pelrun/dtv2ser/arm/Src/uart.c

/*
 * uart.c - serial hw routines
 *
 * This file is part of dtv2ser.
 * See README for copyright notice.
 *
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
 */

#include <stdint.h>

#include "usbd_cdc_if.h"

#include "board.h"

#include "uart.h"
#include "param.h"
#include "display.h"
#include "timer.h"

#define CIRCBUF_SIZE 256

typedef struct
{
  volatile uint16_t in;
  volatile uint16_t out;
  volatile uint8_t data[CIRCBUF_SIZE];
} Circular_Buffer_t;

#define CIRCBUF_LEN(c) ((uint16_t)(c.in - c.out) & (CIRCBUF_SIZE-1))

static inline uint16_t circbuf_len(Circular_Buffer_t *c)
{
  return (c->in - c->out) & (CIRCBUF_SIZE-1);
}

static inline uint16_t circbuf_free(Circular_Buffer_t *c)
{
  return CIRCBUF_SIZE - circbuf_len(c);
}

static inline void circbuf_write(Circular_Buffer_t *c, uint8_t data)
{
  c->data[c->in++ & (CIRCBUF_SIZE-1)] = data;
}

static inline uint8_t circbuf_read(Circular_Buffer_t *c)
{
  return c->data[c->out++ & (CIRCBUF_SIZE-1)];
}

// ---------- init ----------------------------------------------------------

static uint8_t rx_in = 0, rx_out = 0, *rx_buf = NULL;

void uart_init(void)
{
  rx_in = rx_out = 0;
}

// ---------- read ----------------------------------------------------------

uint8_t uart_read_data_available(void)
{
  return rx_in != rx_out;
}

void uart_stop_reception(void)
{
}

void uart_start_reception(void)
{
}

void uart_load_rx(uint8_t *data, uint16_t len)
{
  rx_in = len;
  rx_out = 0;
  rx_buf = data;
}

uint8_t uart_read(uint8_t *data)
{
  timeout_t t = TIMEOUT(PARAM_WORD(PARAM_WORD_SERIAL_READ_AVAIL_TIMEOUT));
  while(rx_in == rx_out) {
    if (timer_expired(&t)) {
      return 0;
    }
    __WFI();
  }

  *data = rx_buf[rx_out++];

  if (rx_in == rx_out)
  {
    // let USB give us another packet
    CDC_Resume_RX();
  }

  return 1;
}

// ---------- send ----------------------------------------------------------
#if 0
static Circular_Buffer_t tx_buf;

void uart_flush(void)
{
  __disable_irq();
  if (tx_buf.in > 0)
  {
    if (CDC_Transmit_FS((uint8_t*)tx_buf.data,tx_buf.in) == USBD_OK)
    {
      tx_buf.in = tx_buf.out = 0;
    }
  }
  __enable_irq();
}

void HAL_SYSTICK_Callback()
{
  static uint16_t wait = 0;
  if ((wait++ & 0xFF) == 0)
  {
    uart_flush();
  }
}

uint8_t uart_send(uint8_t data)
{
  circbuf_write(&tx_buf, data);

  if (data == '\n' || tx_buf.in >= CDC_DATA_FS_MAX_PACKET_SIZE)
  {
    uart_flush();
  }

  return 1;
}

#else

uint8_t uart_send(uint8_t data)
{
  while (CDC_Transmit_FS(&data,1) != USBD_OK);

  return 1;
}

#endif
