pelrun/dtv2ser/server/param.c

/*
 * param.c - parameter handling
 *
 * Written by
 *  Christian Vogelgsang <chris@vogelgsang.org>
 *
 * This file is part of dtv2ser.
 * See README for copyright notice.
 *
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
 */

#include <stdint.h>
#include <avr/eeprom.h>
#include <util/crc16.h>

#include "board.h"

#include "param.h"

// eeprom parameters
parameters_t eeprom_parameters EEMEM;
uint16_t eeprom_crc16 EEMEM;

// default parameters
static parameters_t default_parameters = {
  // 8 bit parameters
  {
    2,        // 0: PARAM_BYTE_DTVLOW_RECV_DELAY count
    5,        // 1: PARAM_BYTE_ERROR_CONDITION_LOOPS count
    0,        // 2: PARAM_BYTE_DIAGNOSE_PATTERN byte
    3,        // 3: PARAM_BYTE_IS_ALIVE_REPEAT count
    2,        // 4: PARAM_BYTE_IS_ALIVE_DELAY 1ms
  },
  // 16 bit parameters
  {
    500,      // 0: PARAM_WORD_DTVLOW_WAIT_FOR_ACK_DELAY 1ms
    10,       // 1: PARAM_WORD_DTVLOW_PREPARE_RESET_DELAY 1ms
    1000,     // 2: PARAM_WORD_DTVLOW_RESET_DELAY 1ms
    500,      // 3: PARAM_WORD_ERROR_CONDITION_DELAY 1ms
    500,      // 4: PARAM_WORD_SERIAL_RTS_TIMEOUT 1ms
    500,      // 5: PARAM_WORD_SERIAL_READ_AVAIL_TIMEOUT 1ms
    500,      // 6: PARAM_WORD_SERIAL_SEND_READY_TIMEOUT 1ms
    0x400,    // 7: PARAM_WORD_DTV_TRANSFER_BLOCK_SIZE bytes
    20,       // 8: PARAM_WORD_IS_ALIVE_IDLE 1ms
  }
};

// current parameters
parameters_t parameters;

// build check sum for parameter block
static uint16_t calc_crc16(parameters_t *p)
{
  uint16_t crc16 = 0xffff;
  uint8_t *data = (uint8_t *)p;
  for(uint16_t i=0;i<sizeof(parameters_t);i++) {
    crc16 = _crc16_update(crc16,*data);
    data++;
  }
  return crc16;
}

uint8_t param_save(void)
{
  // check that eeprom is writable
  if(!eeprom_is_ready())
    return PARAM_EEPROM_NOT_READY;

  // write current parameters to eeprom
  eeprom_write_block(&parameters,&eeprom_parameters,sizeof(parameters_t));

  // calc current parameter crc
  uint16_t crc16 = calc_crc16(&parameters);
  eeprom_write_word(&eeprom_crc16,crc16);

  return PARAM_OK;
}

uint8_t param_load(void)
{
  // check that eeprom is readable
  if(!eeprom_is_ready())
    return PARAM_EEPROM_NOT_READY;

  // read parameters
  parameters_t param;
  eeprom_read_block(&param,&eeprom_parameters,sizeof(parameters_t));

  // read crc16
  uint16_t crc16 = eeprom_read_word(&eeprom_crc16);
  uint16_t my_crc16 = calc_crc16(&param);
  if(crc16 != my_crc16)
    return PARAM_EEPROM_CRC_MISMATCH;

  // set new param
  parameters = param;

  return PARAM_OK;
}

void param_reset(void)
{
  // restore default param
  parameters = default_parameters;
}

void param_init(void)
{
  if(param_load()!=PARAM_OK)
    param_reset();
}
