pelrun/dtv2ser/arm/Src/crc16.c

#include <stdint.h>

uint16_t _crc16_update(uint16_t crc, uint8_t a)
{
  int i;

  crc ^= a;
  for (i = 0; i < 8; ++i)
  {
    if (crc & 1)
      crc = (crc >> 1) ^ 0xA001;
    else
      crc = (crc >> 1);
  }

  return crc;
}
