pelrun/dtv2ser/server/stk500boot.c

/*****************************************************************************
Title:     STK500v2 compatible bootloader
Author:    Peter Fleury <pfleury@gmx.ch>   http://jump.to/fleury
File:      $Id: stk500boot.c 684 2008-10-31 08:59:57Z cnvogelg $
Compiler:  avr-gcc 3.4.5 or 4.1 / avr-libc 1.4.3
Hardware:  All AVRs with bootloader support, tested with ATmega8
License:   GNU General Public License

DESCRIPTION:
    This program allows an AVR with bootloader capabilities to
    read/write its own Flash/EEprom. To enter Programming mode
    an input pin is checked. If this pin is pulled low, programming mode
    is entered. If not, normal execution is done from $0000
    "reset" vector in Application area.
    Size < 500 words, fits into a 512 word bootloader section
	when compiled with avr-gcc 4.1

USAGE:
    - Set AVR MCU type and clock-frequency (F_CPU) in the Makefile.
    - Set baud rate below (AVRISP only works with 115200 bps)
    - compile/link the bootloader with the supplied Makefile
    - program the "Boot Flash section size" (BOOTSZ fuses),
      for boot-size 512 words:  program BOOTSZ1
    - enable the BOOT Reset Vector (program BOOTRST)
    - Upload the hex file to the AVR using any ISP programmer
    - Program Boot Lock Mode 3 (program BootLock 11 and BootLock 12 lock bits)
    - Reset your AVR while keeping PROG_PIN pulled low
    - Start AVRISP Programmer (AVRStudio/Tools/Program AVR)
    - AVRISP will detect the bootloader
    - Program your application FLASH file and optional EEPROM file using AVRISP

Note:
    Erasing the device without flashing, through AVRISP GUI button "Erase Device"
    is not implemented, due to AVRStudio limitations.
    Flash is always erased before programming.

	AVRdude:
	Please uncomment #define REMOVE_CMD_SPI_MULTI when using AVRdude.
	Comment #define REMOVE_PROGRAM_LOCK_BIT_SUPPORT to reduce code size
	Read Fuse Bits and Read/Write Lock Bits is not supported

NOTES:
    Based on Atmel Application Note AVR109 - Self-programming
    Based on Atmel Application Note AVR068 - STK500v2 Protocol

LICENSE:
    Copyright (C) 2006 Peter Fleury

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
*****************************************************************************/
#include <inttypes.h>
#include <avr/io.h>
#include <avr/interrupt.h>
#include <avr/boot.h>
#include <avr/pgmspace.h>
#include "stk500boot.h"

/*
 * Uncomment the following lines to save code space
 */
#define REMOVE_PROGRAM_LOCK_BIT_SUPPORT  // disable program lock bits
//#define REMOVE_BOOTLOADER_LED            // no LED to show active bootloader
//#define REMOVE_PROG_PIN_PULLUP           // disable internal pullup, use external
//#define REMOVE_CMD_SPI_MULTI             // disable processing of SPI_MULTI commands

/*
 * Pin "PROG_PIN" on port "PROG_PORT" has to be pulled low
 * (active low) to start the bootloader
 * uncomment #define REMOVE_PROG_PIN_PULLUP if using an external pullup
 */
#define PROG_PORT  PORTB
#define PROG_DDR   DDRB
#define PROG_IN    PINB
#define PROG_PIN   PINB4

/*
 * Active-low LED on pin "PROGLED_PIN" on port "PROGLED_PORT"
 * indicates that bootloader is active
 */
#define PROGLED_PORT PORTB
#define PROGLED_DDR  DDRB
#define PROGLED_PIN  PINB1

/*
 * define CPU frequency in Mhz here if not defined in Makefile
 */
#ifndef F_CPU
#define F_CPU 7372800UL
#endif


/*
 * UART Baudrate, AVRStudio AVRISP only accepts 115200 bps
 */
#ifndef BAUDRATE
#define BAUDRATE 115200
#endif

/*
 *  Enable (1) or disable (0) USART double speed operation
 */
#define UART_BAUDRATE_DOUBLE_SPEED 0


/*
 * HW and SW version, reported to AVRISP, must match version of AVRStudio
 */
#define CONFIG_PARAM_BUILD_NUMBER_LOW	0
#define CONFIG_PARAM_BUILD_NUMBER_HIGH	0
#define CONFIG_PARAM_HW_VER				0x0F
#define CONFIG_PARAM_SW_MAJOR			2
#define CONFIG_PARAM_SW_MINOR			0x0A



/*
 * Calculate the address where the bootloader starts from FLASHEND and BOOTSIZE
 * (adjust BOOTSIZE below and BOOTLOADER_ADDRESS in Makefile if you want to change the size of the bootloader)
 */
#define BOOTSIZE 512
#define APP_END  (FLASHEND -(2*BOOTSIZE) + 1)



/*
 * Signature bytes are not available in avr-gcc io_xxx.h
 */
#if defined (__AVR_ATmega8__)
    #define SIGNATURE_BYTES 0x1E9307
#elif defined (__AVR_ATmega16__)
    #define SIGNATURE_BYTES 0x1E9403
#elif defined (__AVR_ATmega32__)
    #define SIGNATURE_BYTES 0x1E9502
#elif defined (__AVR_ATmega8515__)
    #define SIGNATURE_BYTES 0x1E9306
#elif defined (__AVR_ATmega8535__)
    #define SIGNATURE_BYTES 0x1E9308
#elif defined (__AVR_ATmega88__)
    #define SIGNATURE_BYTES 0x1E930A
#elif defined (__AVR_ATmega162__)
    #define SIGNATURE_BYTES 0x1E9404
#elif defined (__AVR_ATmega168__)
    #define SIGNATURE_BYTES 0x1E9406
#elif defined (__AVR_ATmega128__)
    #define SIGNATURE_BYTES 0x1E9702
#else
	#error "no signature definition for MCU available"
#endif


/*
 *  Defines for the various USART registers
 */
#if  defined(__AVR_ATmega8__)    || defined(__AVR_ATmega16__) || defined(__AVR_ATmega32__) \
  || defined(__AVR_ATmega8515__) || defined(__AVR_ATmega8535__) \
/* ATMega8 with one USART */
#define	UART_BAUD_RATE_LOW	     UBRRL
#define	UART_STATUS_REG	         UCSRA
#define	UART_CONTROL_REG	     UCSRB
#define	UART_ENABLE_TRANSMITTER	 TXEN
#define	UART_ENABLE_RECEIVER	 RXEN
#define	UART_TRANSMIT_COMPLETE	 TXC
#define	UART_RECEIVE_COMPLETE	 RXC
#define	UART_DATA_REG	         UDR
#define UART_DOUBLE_SPEED        U2X

#elif  defined(__AVR_ATmega64__) || defined(__AVR_ATmega128__) || defined(__AVR_ATmega162__) || defined(__AVR_ATmega88__) || defined(__AVR_ATmega168__)
/* ATMega with two USART */
#define	UART_BAUD_RATE_LOW	     UBRR0L
#define	UART_STATUS_REG	         UCSR0A
#define	UART_CONTROL_REG	     UCSR0B
#define	UART_ENABLE_TRANSMITTER	 TXEN0
#define	UART_ENABLE_RECEIVER	 RXEN0
#define	UART_TRANSMIT_COMPLETE	 TXC0
#define	UART_RECEIVE_COMPLETE	 RXC0
#define	UART_DATA_REG	         UDR0
#define UART_DOUBLE_SPEED        U2X0

#else
	#error "no UART definition for MCU available"
#endif


/*
 * Macros to map the new ATmega88/168 EEPROM bits
 */
#ifdef EEMPE
#define EEMWE EEMPE
#define EEWE  EEPE
#endif


/*
 * Macro to calculate UBBR from XTAL and baudrate
 */
#if UART_BAUDRATE_DOUBLE_SPEED
#define UART_BAUD_SELECT(baudRate,xtalCpu) (((float)(xtalCpu))/(((float)(baudRate))*8.0)-1.0+0.5)
#else
#define UART_BAUD_SELECT(baudRate,xtalCpu) (((float)(xtalCpu))/(((float)(baudRate))*16.0)-1.0+0.5)
#endif


/*
 * States used in the receive state machine
 */
#define	ST_START		0
#define	ST_GET_SEQ_NUM	1
#define ST_MSG_SIZE_1	2
#define ST_MSG_SIZE_2	3
#define ST_GET_TOKEN	4
#define ST_GET_DATA		5
#define	ST_GET_CHECK	6
#define	ST_PROCESS		7


/*
 * use 16bit address variable for ATmegas with <= 64K flash
 */
#if defined(RAMPZ)
typedef uint32_t address_t;
#else
typedef uint16_t address_t;
#endif


/*
 * function prototypes
 */
static void sendchar(char c);
static unsigned char recchar(void);


/*
 * since this bootloader is not linked against the avr-gcc crt1 functions,
 * to reduce the code size, we need to provide our own initialization
 */
void __jumpMain     (void) __attribute__ ((naked)) __attribute__ ((section (".init9")));

void __jumpMain(void)
{
    asm volatile ( ".set __stack, %0" :: "i" (RAMEND) );
    asm volatile ( "clr __zero_reg__" );                       // GCC depends on register r1 set to 0
    asm volatile ( "out %0, __zero_reg__" :: "I" (_SFR_IO_ADDR(SREG)) );  // set SREG to 0
    asm volatile ( "rjmp main");                               // jump to main()
}


/*
 * send single byte to USART, wait until transmission is completed
 */
static void sendchar(char c)
{
    UART_DATA_REG = c;                                   // prepare transmission
    while (!(UART_STATUS_REG & (1 << UART_TRANSMIT_COMPLETE)));// wait until byte sent
    UART_STATUS_REG |= (1 << UART_TRANSMIT_COMPLETE);          // delete TXCflag
}

/*
 * Read single byte from USART, block if no data available
 */
static unsigned char recchar(void)
{
    while(!(UART_STATUS_REG & (1 << UART_RECEIVE_COMPLETE)));  // wait for data
    return UART_DATA_REG;
}



int main(void)
{
  address_t       address = 0;
  address_t       eraseAddress = 0;
  unsigned char   msgParseState;
  unsigned int    i = 0;
  unsigned char   checksum = 0;
  unsigned char   seqNum = 0;
  unsigned int    msgLength = 0;
  unsigned char   msgBuffer[285];
  unsigned char   c, *p;


  /*
  * Branch to bootloader or application code ?
   */
#ifndef REMOVE_PROG_PIN_PULLUP
    PROG_PORT |= (1<<PROG_PIN);		// Enable internal pullup
  asm volatile ("nop");           // wait until port has changed
#endif
  if(!(PROG_IN & (1<<PROG_PIN)))
  {
#ifndef REMOVE_BOOTLOADER_LED
        /* PROG_PIN pulled low, indicate with LED that bootloader is active */
    PROGLED_DDR  |= (1<<PROGLED_PIN);
    PROGLED_PORT &= ~(1<<PROGLED_PIN);
#endif
        /*
    * Init UART
      * set baudrate and enable USART receiver and transmiter without interrupts
         */
#if UART_BAUDRATE_DOUBLE_SPEED
      UART_STATUS_REG   |=  (1 <<UART_DOUBLE_SPEED);
#endif
    UART_BAUD_RATE_LOW = UART_BAUD_SELECT(BAUDRATE,F_CPU);
    UART_CONTROL_REG   = (1 << UART_ENABLE_RECEIVER) | (1 << UART_ENABLE_TRANSMITTER);


        /* main loop */
    for(;;)
    {
            /*
      * Collect received bytes to a complete message
             */
        msgParseState = ST_START;
      while ( msgParseState != ST_PROCESS )
      {
        c = recchar();
        switch (msgParseState)
        {
          case ST_START:
          if( c == MESSAGE_START )
          {
            msgParseState = ST_GET_SEQ_NUM;
            checksum = MESSAGE_START^0;
          }
          break;

          case ST_GET_SEQ_NUM:
          if ( (c == 1) || (c == seqNum) )
          {
            seqNum = c;
            msgParseState = ST_MSG_SIZE_1;
            checksum ^= c;
          }
          else
          {
            msgParseState = ST_START;
          }
          break;

          case ST_MSG_SIZE_1:
          msgLength = c<<8;
          msgParseState = ST_MSG_SIZE_2;
          checksum ^= c;
          break;

          case ST_MSG_SIZE_2:
          msgLength |= c;
          msgParseState = ST_GET_TOKEN;
          checksum ^= c;
          break;

          case ST_GET_TOKEN:
          if ( c == TOKEN )
          {
            msgParseState = ST_GET_DATA;
            checksum ^= c;
            i = 0;
          }
          else
          {
            msgParseState = ST_START;
          }
          break;

          case ST_GET_DATA:
          msgBuffer[i++] = c;
          checksum ^= c;
          if ( i == msgLength )
          {
            msgParseState = ST_GET_CHECK;
          }
          break;

          case ST_GET_CHECK:
          if( c == checksum )
          {
            msgParseState = ST_PROCESS;
          }
          else
          {
            msgParseState = ST_START;
          }
          break;
        }//switch
      }//while(msgParseState)

      /*
      * Now process the STK500 commands, see Atmel Appnote AVR068
       */

        switch (msgBuffer[0])
      {
#ifndef REMOVE_CMD_SPI_MULTI
        case CMD_SPI_MULTI:
        {
          unsigned char answerByte = 0;

                    // only Read Signature Bytes implemented, return dummy value for other instructions
          if ( msgBuffer[4]== 0x30 )
          {
            unsigned char signatureIndex = msgBuffer[6];

            if ( signatureIndex == 0 )
              answerByte = (SIGNATURE_BYTES >>16) & 0x000000FF;
            else if ( signatureIndex == 1 )
              answerByte = (SIGNATURE_BYTES >> 8) & 0x000000FF;
            else
              answerByte = SIGNATURE_BYTES & 0x000000FF;
          }
          msgLength = 7;
          msgBuffer[1] = STATUS_CMD_OK;
          msgBuffer[2] = 0;
          msgBuffer[3] = msgBuffer[4];  // Instruction Byte 1
          msgBuffer[4] = msgBuffer[5];  // Instruction Byte 2
          msgBuffer[5] = answerByte;
          msgBuffer[6] = STATUS_CMD_OK;
        }
        break;
#endif
        case CMD_SIGN_ON:
        msgLength = 11;
        msgBuffer[1]  = STATUS_CMD_OK;
        msgBuffer[2]  = 8;
        msgBuffer[3]  = 'A';
        msgBuffer[4]  = 'V';
        msgBuffer[5]  = 'R';
        msgBuffer[6]  = 'I';
        msgBuffer[7]  = 'S';
        msgBuffer[8]  = 'P';
        msgBuffer[9]  = '_';
        msgBuffer[10] = '2';
        break;

        case CMD_GET_PARAMETER:
        {
          unsigned char value;

          switch(msgBuffer[1])
          {
            case PARAM_BUILD_NUMBER_LOW:
            value = CONFIG_PARAM_BUILD_NUMBER_LOW;
            break;
            case PARAM_BUILD_NUMBER_HIGH:
            value = CONFIG_PARAM_BUILD_NUMBER_HIGH;
            break;
            case PARAM_HW_VER:
            value = CONFIG_PARAM_HW_VER;
            break;
            case PARAM_SW_MAJOR:
            value = CONFIG_PARAM_SW_MAJOR;
            break;
            case PARAM_SW_MINOR:
            value = CONFIG_PARAM_SW_MINOR;
            break;
            default:
            value = 0;
            break;
          }
          msgLength = 3;
          msgBuffer[1] = STATUS_CMD_OK;
          msgBuffer[2] = value;
        }
        break;

        case CMD_SET_PARAMETER:
        case CMD_ENTER_PROGMODE_ISP:
        case CMD_LEAVE_PROGMODE_ISP:
        msgLength = 2;
        msgBuffer[1] = STATUS_CMD_OK;
        break;

        case CMD_READ_SIGNATURE_ISP:
        {
          unsigned char signatureIndex = msgBuffer[4];
          unsigned char signature;

          if ( signatureIndex == 0 )
            signature = (SIGNATURE_BYTES >>16) & 0x000000FF;
          else if ( signatureIndex == 1 )
            signature = (SIGNATURE_BYTES >> 8) & 0x000000FF;
          else
            signature = SIGNATURE_BYTES & 0x000000FF;

          msgLength = 4;
          msgBuffer[1] = STATUS_CMD_OK;
          msgBuffer[2] = signature;
          msgBuffer[3] = STATUS_CMD_OK;
        }
        break;

        case CMD_READ_LOCK_ISP:
        msgLength = 4;
        msgBuffer[1] = STATUS_CMD_OK;
        msgBuffer[2] = boot_lock_fuse_bits_get( GET_LOCK_BITS );
        msgBuffer[3] = STATUS_CMD_OK;
        break;

        case CMD_READ_FUSE_ISP:
        {
          unsigned char fuseBits;

          if ( msgBuffer[2] == 0x50 )
          {
            if ( msgBuffer[3] == 0x08 )
              fuseBits = boot_lock_fuse_bits_get( GET_EXTENDED_FUSE_BITS );
            else
              fuseBits = boot_lock_fuse_bits_get( GET_LOW_FUSE_BITS );
          }
          else
          {
            fuseBits = boot_lock_fuse_bits_get( GET_HIGH_FUSE_BITS );
          }
          msgLength = 4;
          msgBuffer[1] = STATUS_CMD_OK;
          msgBuffer[2] = fuseBits;
          msgBuffer[3] = STATUS_CMD_OK;
        }
        break;

#ifndef REMOVE_PROGRAM_LOCK_BIT_SUPPORT
        case CMD_PROGRAM_LOCK_ISP:
        {
          unsigned char lockBits = msgBuffer[4];

          lockBits = (~lockBits) & 0x3C;  // mask BLBxx bits
          boot_lock_bits_set(lockBits);	// and program it
          boot_spm_busy_wait();

          msgLength = 3;
          msgBuffer[1] = STATUS_CMD_OK;
          msgBuffer[2] = STATUS_CMD_OK;
        }
        break;
#endif
        case CMD_CHIP_ERASE_ISP:
        eraseAddress = 0;
        msgLength = 2;
        msgBuffer[1] = STATUS_CMD_OK;
        break;

        case CMD_LOAD_ADDRESS:
#if defined(RAMPZ)
        address = ( ((address_t)(msgBuffer[1])<<24)|((address_t)(msgBuffer[2])<<16)|((address_t)(msgBuffer[3])<<8)|(msgBuffer[4]) )<<1;
#else
        address = ( ((msgBuffer[3])<<8)|(msgBuffer[4]) )<<1;  //convert word to byte address
#endif
        msgLength = 2;
        msgBuffer[1] = STATUS_CMD_OK;
        break;

        case CMD_PROGRAM_FLASH_ISP:
        case CMD_PROGRAM_EEPROM_ISP:
        {
          unsigned int  size = ((msgBuffer[1])<<8) | msgBuffer[2];
          unsigned char *p = msgBuffer+10;
          unsigned int  data;
          unsigned char highByte, lowByte;
          address_t     tempaddress = address;


          if ( msgBuffer[0] == CMD_PROGRAM_FLASH_ISP )
          {
                    // erase only main section (bootloader protection)
            if  (  eraseAddress < APP_END )
            {
              boot_page_erase(eraseAddress);	// Perform page erase
              boot_spm_busy_wait();		// Wait until the memory is erased.
              eraseAddress += SPM_PAGESIZE;    // point to next page to be erase
            }

                    /* Write FLASH */
            do {
              lowByte   = *p++;
              highByte  = *p++;

              data =  (highByte << 8) | lowByte;
              boot_page_fill(address,data);

              address = address + 2;  	// Select next word in memory
              size -= 2;			// Reduce number of bytes to write by two
            } while(size);			// Loop until all bytes written

            boot_page_write(tempaddress);
            boot_spm_busy_wait();
            boot_rww_enable();				// Re-enable the RWW section
          }
          else
          {
                    /* write EEPROM */
            do {
              EEARL = address;			// Setup EEPROM address
              EEARH = (address >> 8);
              address++;					// Select next EEPROM byte

              EEDR= *p++;				    // get byte from buffer
              EECR |= (1<<EEMWE);			// Write data into EEPROM
              EECR |= (1<<EEWE);

              while (EECR & (1<<EEWE));	// Wait for write operation to finish
              size--;						// Decrease number of bytes to write
            } while(size);					// Loop until all bytes written
          }
          msgLength = 2;
          msgBuffer[1] = STATUS_CMD_OK;
        }
        break;

        case CMD_READ_FLASH_ISP:
        case CMD_READ_EEPROM_ISP:
        {
          unsigned int  size = ((msgBuffer[1])<<8) | msgBuffer[2];
          unsigned char *p = msgBuffer+1;
          msgLength = size+3;

          *p++ = STATUS_CMD_OK;
          if (msgBuffer[0] == CMD_READ_FLASH_ISP )
          {
            unsigned int data;

                        // Read FLASH
            do {
#if defined(RAMPZ)
              data = pgm_read_word_far(address);
#else
              data = pgm_read_word_near(address);
#endif
              *p++ = (unsigned char)data;         //LSB
              *p++ = (unsigned char)(data >> 8);	//MSB
              address    += 2;  	 // Select next word in memory
              size -= 2;
            }while (size);
          }
          else
          {
                    /* Read EEPROM */
            do {
              EEARL = address;			// Setup EEPROM address
              EEARH = ((address >> 8));
              address++;					// Select next EEPROM byte
              EECR |= (1<<EERE);			// Read EEPROM
              *p++ = EEDR;				// Send EEPROM data
              size--;
            }while(size);
          }
          *p++ = STATUS_CMD_OK;
        }
        break;

        default:
        msgLength = 2;
        msgBuffer[1] = STATUS_CMD_FAILED;
        break;
      }

            /*
      * Now send answer message back
             */
        sendchar(MESSAGE_START);
      checksum = MESSAGE_START^0;

      sendchar(seqNum);
      checksum ^= seqNum;

      c = ((msgLength>>8)&0xFF);
      sendchar(c);
      checksum ^= c;

      c = msgLength&0x00FF;
      sendchar(c);
      checksum ^= c;

      sendchar(TOKEN);
      checksum ^= TOKEN;

      p = msgBuffer;
      while ( msgLength )
      {
        c = *p++;
        sendchar(c);
        checksum ^=c;
        msgLength--;
      }
      sendchar(checksum);
      seqNum++;

    }//for

#ifndef REMOVE_BOOTLOADER_LED
    PROGLED_DDR  &= ~(1<<PROGLED_PIN);   // set to default
#endif
  }

  /*
  * Now leave bootloader
   */
#ifndef REMOVE_PROG_PIN_PULLUP
    PROG_PORT &= ~(1<<PROG_PIN);    // set to default
#endif
  boot_rww_enable();              // enable application section

  asm volatile ( "push r1" "\n\t"  // Jump to Reset vector in Application Section
    "push r1" "\n\t"
    "ret"     "\n\t"
    ::);

     /*
  * Never return to stop GCC to generate exit return code
    * Actually we will never reach this point, but the compiler doesn't
    * understand this
     */
    for(;;);
}
