pelrun/dtv2ser/server/util.c

/*
 * util.c - utilities
 *
 * Written by
 *  Christian Vogelgsang <chris@vogelgsang.org>
 *
 * This file is part of dtv2ser.
 * See README for copyright notice.
 *
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
 */

#include <stdint.h>

#include "board.h"

#include "util.h"

// convert to hex

uint8_t nybble_to_hex(uint8_t in)
{
  if(in<10)
    return '0' + in;
  else
    return 'A' + in - 10;
}

void byte_to_hex(uint8_t in,uint8_t *out)
{
  out[0] = nybble_to_hex(in >> 4);
  out[1] = nybble_to_hex(in & 0xf);
}

void word_to_hex(uint16_t in,uint8_t *out)
{
  byte_to_hex((uint8_t)(in>>8),out);
  byte_to_hex((uint8_t)(in&0xff),out+2);
}

void dword_to_hex6(uint32_t addr,uint8_t *out)
{
  byte_to_hex((uint8_t)(addr>>16),out);
  word_to_hex((uint16_t)(addr&0xffff),out+2);
}

// parse

uint8_t parse_nybble(uint8_t c,uint8_t *value)
{
  if((c>='a')&&(c<='f')) {
    *value = c + 10 - 'a';
    return 1;
  }
  else if((c>='A')&&(c<='F')) {
    *value = c + 10 - 'A';
    return 1;
  }
  else if((c>='0')&&(c<='9')) {
    *value = c - '0';
    return 1;
  }
  else
    return 0;
}

uint8_t parse_byte(uint8_t *str,uint8_t *value)
{
  uint8_t val;
  if(!parse_nybble(str[0],&val))
    return 0;
  val <<= 4;
  if(!parse_nybble(str[1],value))
    return 0;
  *value |= val;
  return 1;
}

uint8_t parse_word(uint8_t *str,uint16_t *value)
{
  uint8_t val;
  if(!parse_byte(&str[0],&val))
    return 0;
  uint8_t val2;
  if(!parse_byte(&str[2],&val2))
    return 0;
  *value = (uint16_t)val << 8 | val2;
  return 1;
}

uint8_t parse_dword6(uint8_t *str,uint32_t *value)
{
  uint8_t val;
  if(!parse_byte(&str[0],&val))
    return 0;
  uint8_t val2;
  if(!parse_byte(&str[2],&val2))
    return 0;
  uint8_t val3;
  if(!parse_byte(&str[4],&val3))
    return 0;
  *value = (uint32_t)val << 16 | (uint32_t)val2 << 8 | val3;
  return 1;
}
